zzemu-cn/LASER310_FPGA/doc/cn/pic3.png

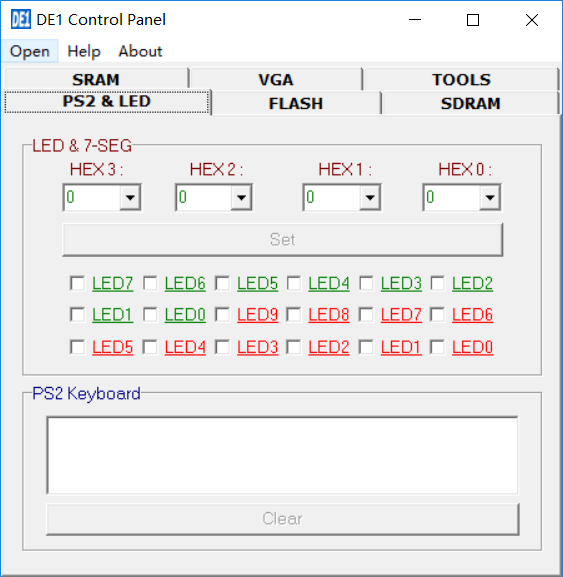
doc/cn/pic3.png
