zzemu-cn/LASER310_FPGA/doc_LASER310/QQ图片20181231125615.png

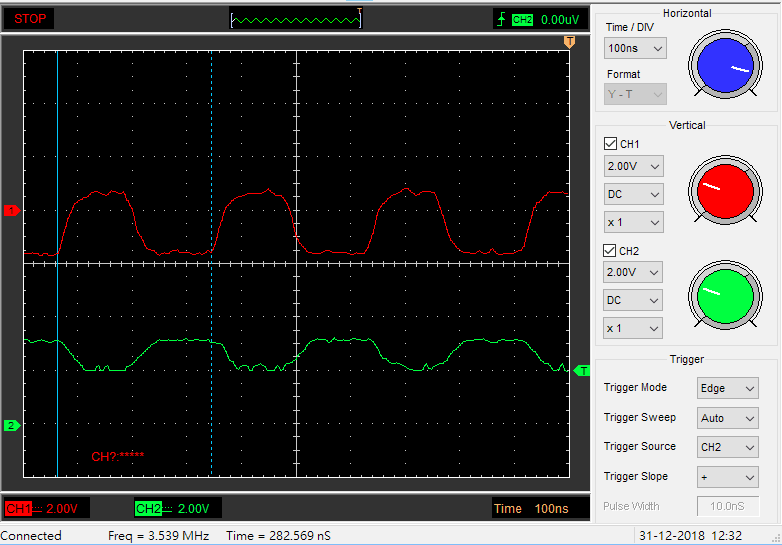
doc_LASER310/QQ图片20181231125615.png
