zzemu-cn/LASER310_FPGA/doc_LASER310/录音磁带/LASER310_cas_0xAA_Figure.png

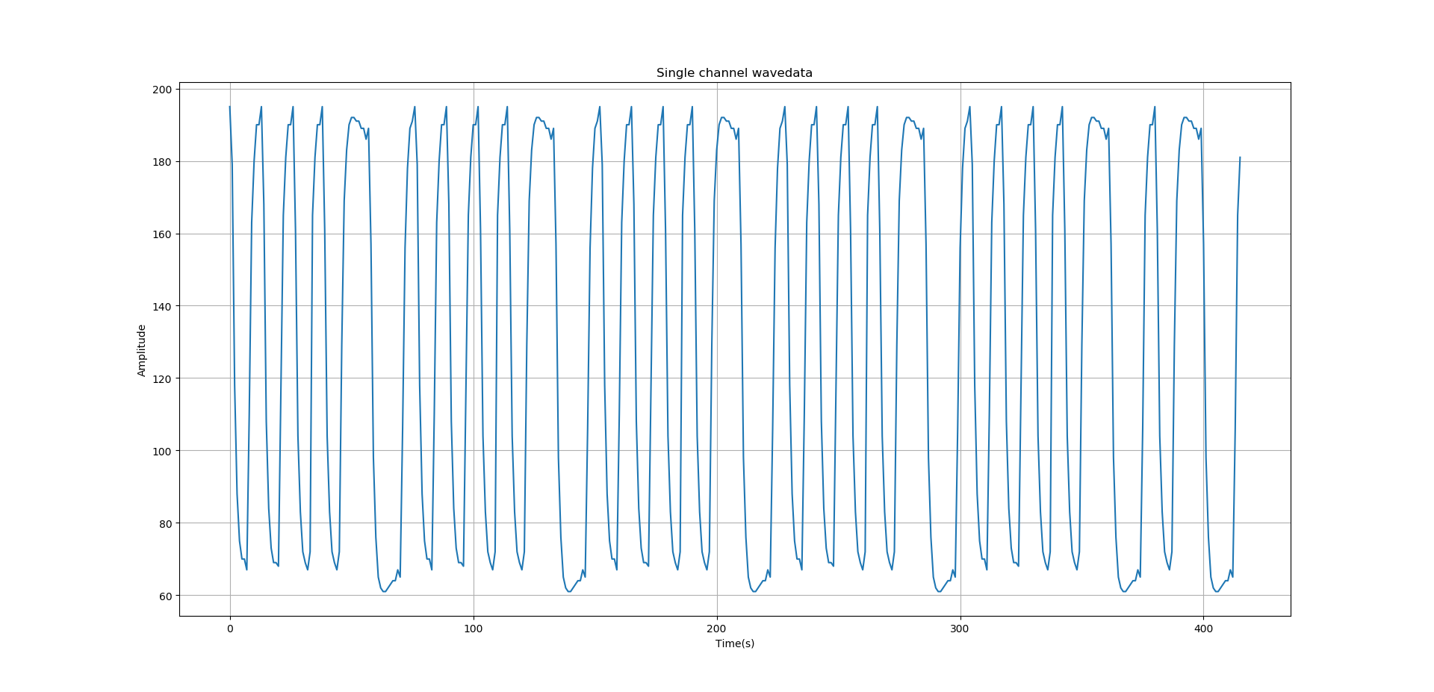
doc_LASER310/录音磁带/LASER310_cas_0xAA_Figure.png
