zzemu-cn/LASER310_FPGA/doc_LASER310/录音磁带/数据磁带机.png

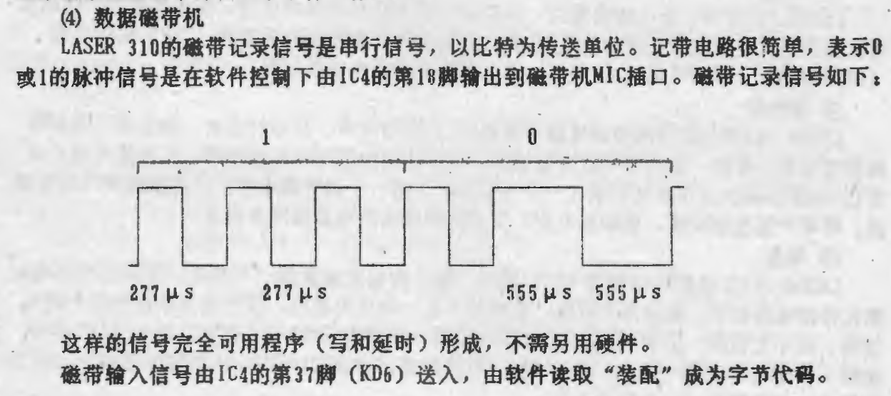
doc_LASER310/录音磁带/数据磁带机.png
