zzemu-cn/LASER310_FPGA/vz/manuals/01.bmp

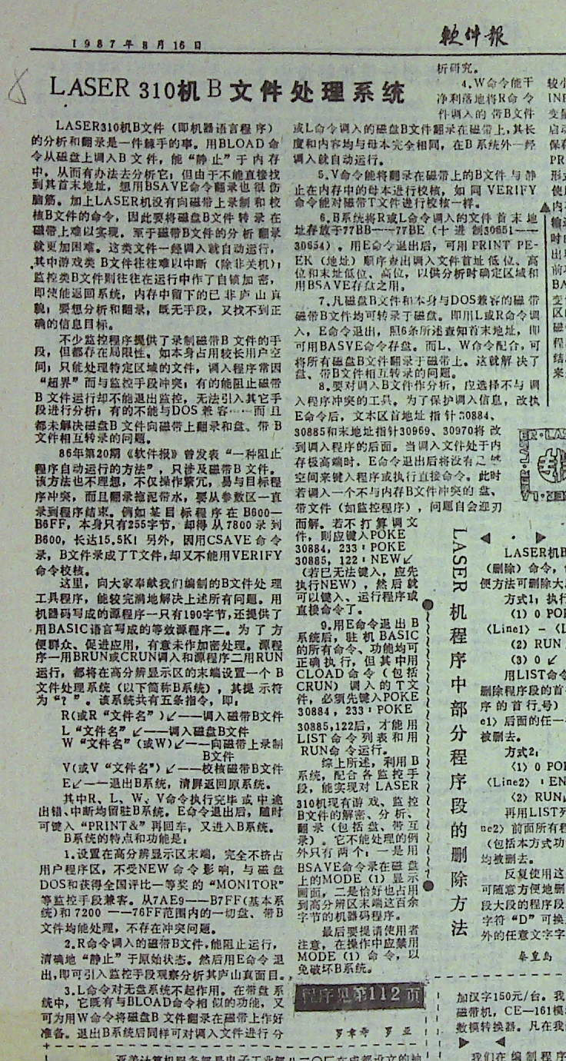
vz/manuals/01.bmp
