zzemu-cn/LASER310_FPGA/vz/manuals/02.png

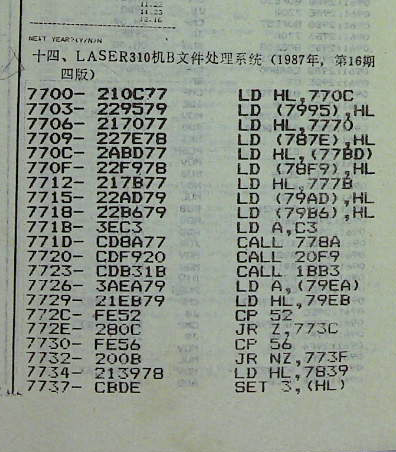
vz/manuals/02.png
